kylenahas/logicanalyzer/Firmware/LogicAnalyzer/LogicAnalyzer_Build_Settings.h

#ifndef __BUILD_SETTINGS__
    #define __BUILD_SETTINGS__

    #define FIRMWARE_VERSION "V5_1"

    //Select the board type to build the firmware for
    //#define BUILD_PICO
    //#define BUILD_PICO_W
    #define BUILD_PICO_W_WIFI
    //#define BUILD_ZERO

#endif
